OPEnSLab-OSU/OPEnS-Hub_Frontiers/Wiring/PCBConnection.jpg

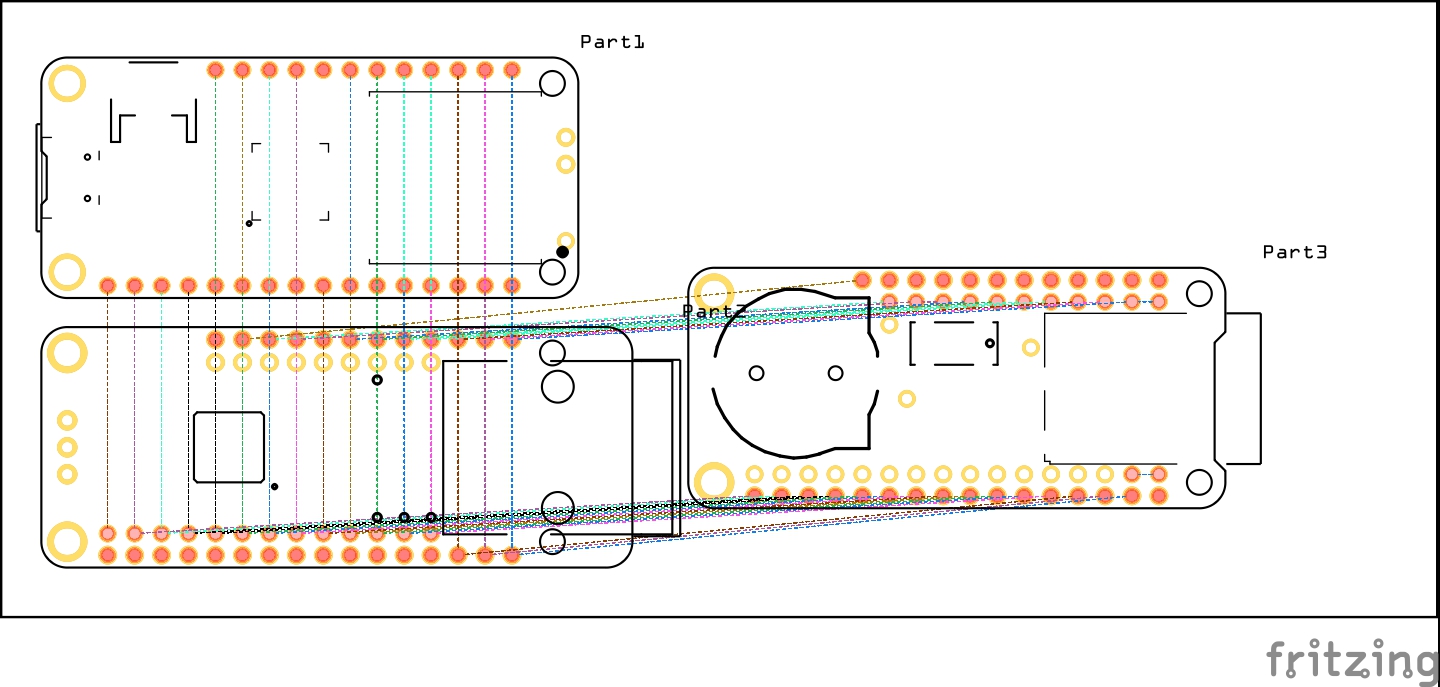
Wiring/PCBConnection.jpg
